cmsc-stageworks/Logic-Re-Initialization-Panel/Mainboard SD Example/Puzzles/AIR_SCRUBBERS/prompt.bmp

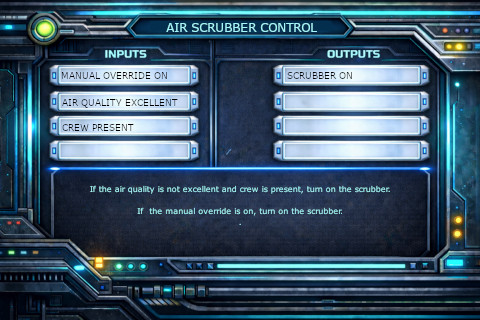
Mainboard SD Example/Puzzles/AIR_SCRUBBERS/prompt.bmp
