cmsc-stageworks/Logic-Re-Initialization-Panel/3D Models/Isolinear Chips NFC/Iso Card Diffuser V2.stl

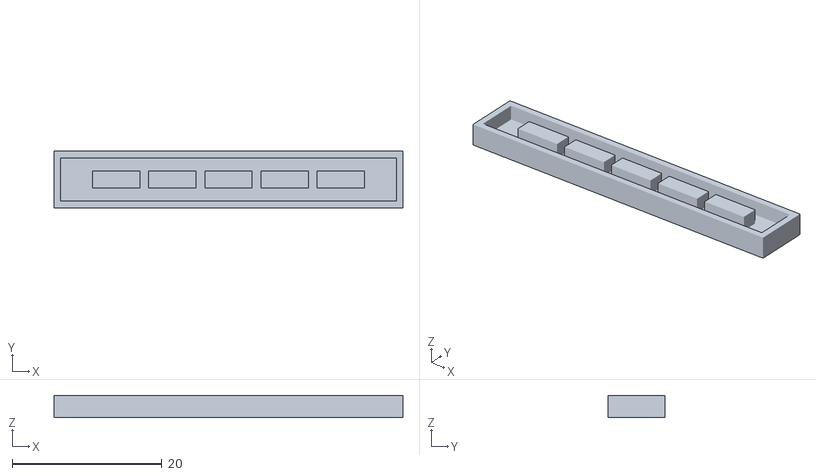
[picture p21: CAD file, 2025-12-29]
3D Models/Isolinear Chips NFC/Iso Card Diffuser V2.stl
46.6 x 7.60 x 3.00
