cmsc-stageworks/Logic-Re-Initialization-Panel/3D Models/Isolinear Chips/PCB REV1.stl

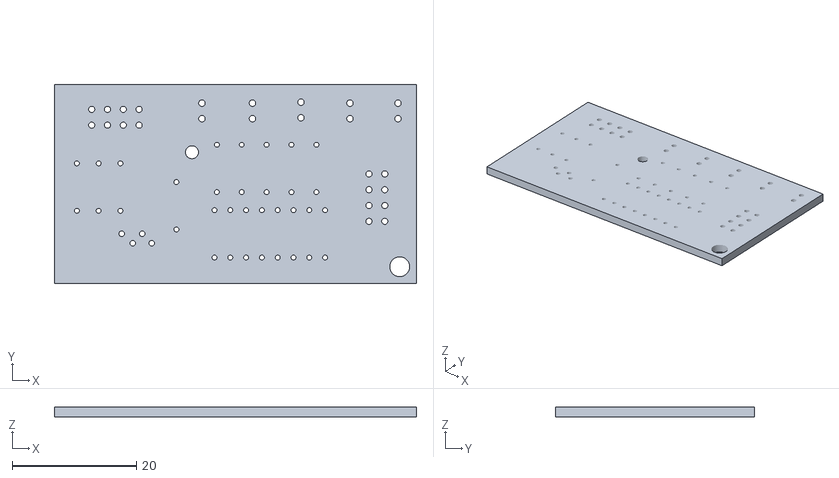
[picture p22: CAD file, 2025-09-20]
3D Models/Isolinear Chips/PCB REV1.stl
58.2 x 32.0 x 1.60
