cmsc-stageworks/Logic-Re-Initialization-Panel/3D Models/Logic Panel/Splitter.stl

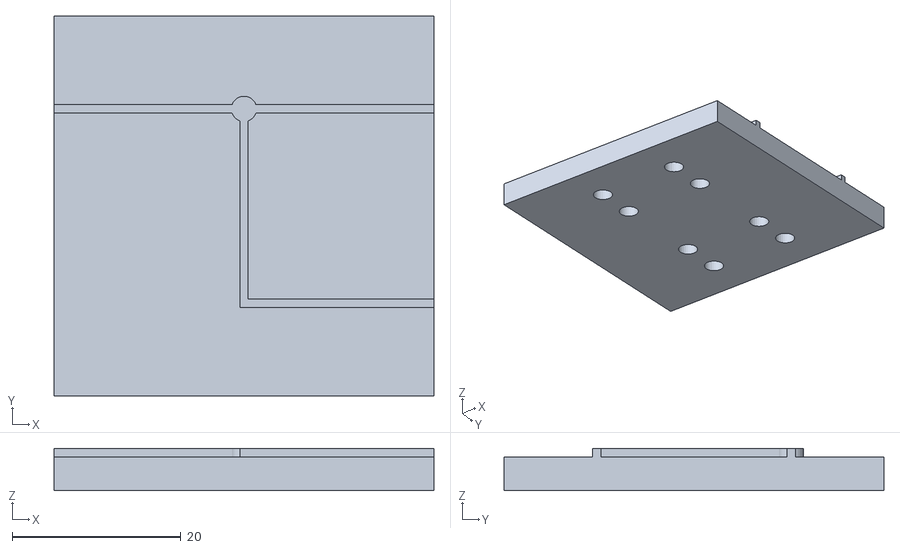
[picture p23: CAD file, 2025-09-20]
3D Models/Logic Panel/Splitter.stl
45.0 x 45.0 x 5.00
