cmsc-stageworks/Logic-Re-Initialization-Panel/Isolinear Chip Board/Isolinear Board PCB/Isolinear Board PCB BARE.step

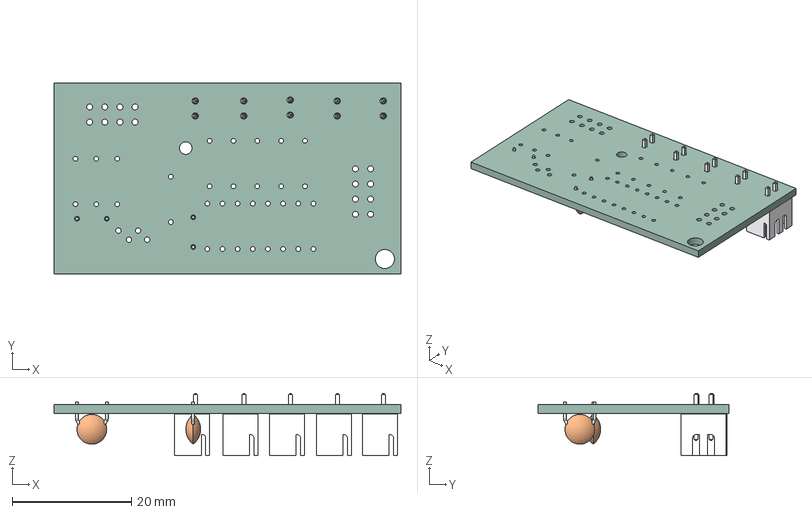
[picture p24: CAD file, 2025-09-20]
Isolinear Chip Board/Isolinear Board PCB/Isolinear Board PCB BARE.step
58.2 x 32.0 x 10.4 mm
JST B2B-XH-A Through-hole shrouded header top entry type x 5
C_Disc_D5.0mm_W2.5mm_P5.00mm x 2
Isolinear Board PCB_PCB
