cmsc-stageworks/Logic-Re-Initialization-Panel/Logic Gates/Logic board magnetic sensor/Logic board magnetic sensor.step

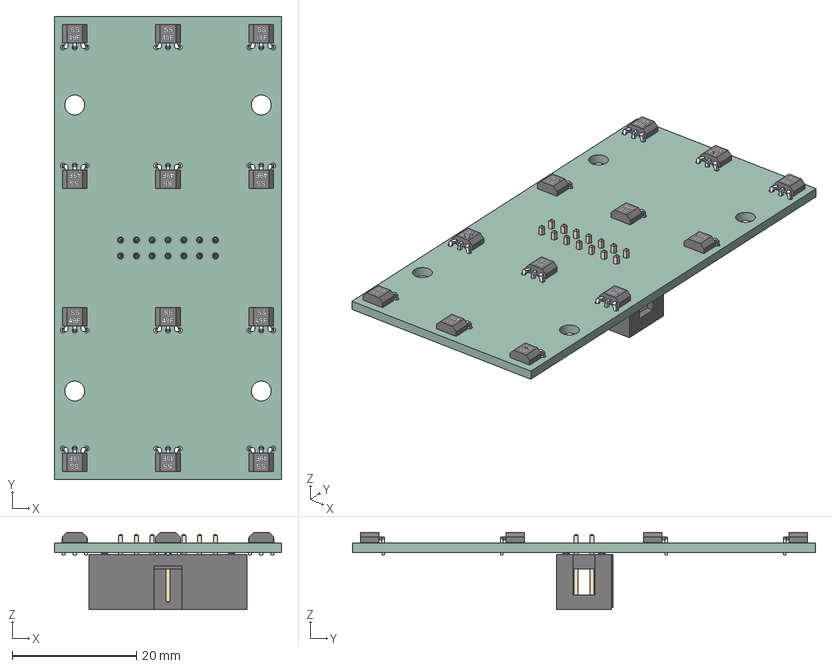
[picture p25: CAD file, 2025-09-20]
Logic Gates/Logic board magnetic sensor/Logic board magnetic sensor.step
36.5 x 74.5 x 12.4 mm
SS49E 90 degree bend x 12
IDC-Header_2x07_P2.54mm_Vertical
Logic board magnetic sensor_PCB
