cmsc-stageworks/Logic-Re-Initialization-Panel/ST7796S Display v7.step

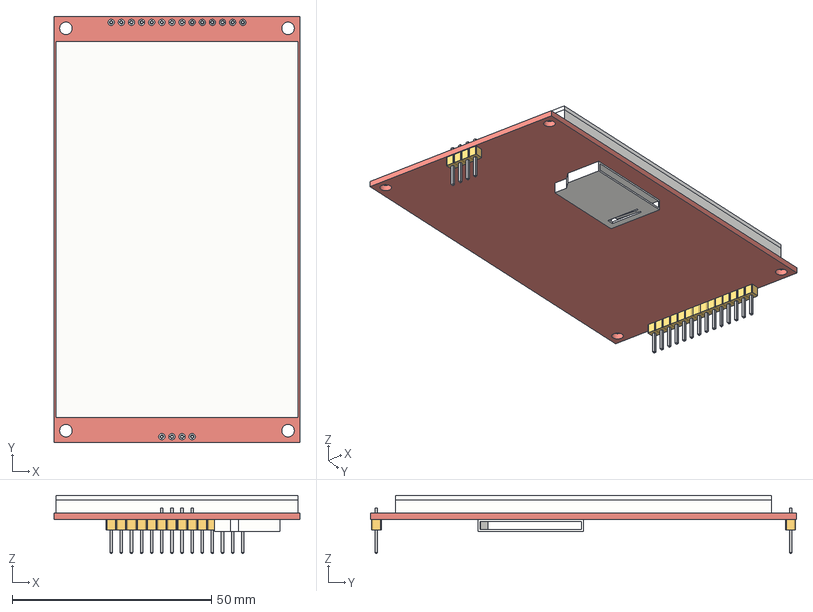
[picture p26: CAD file, 2025-10-08]
ST7796S Display v7.step
61.8 x 107.0 x 14.7 mm
Glass
TFT Screen 480x320
Annular Rings
SD Card
Pins
