cmsc-stageworks/Logic-Re-Initialization-Panel/3D Models/Isolinear Chips/Card Bare Minimum.stl

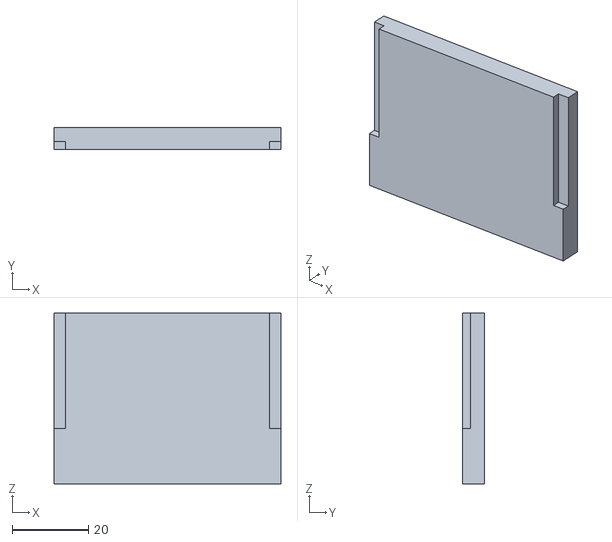
[picture p27: CAD file, 2025-09-20]
3D Models/Isolinear Chips/Card Bare Minimum.stl
59.7 x 5.70 x 44.9
