cmsc-stageworks/Logic-Re-Initialization-Panel/3D Models/Logic Panel/XOR Gate.stl

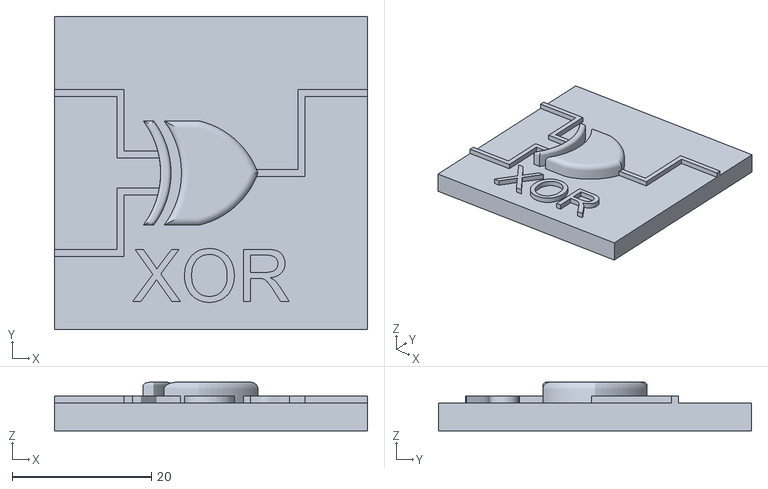
[picture p28: CAD file, 2025-09-20]
3D Models/Logic Panel/XOR Gate.stl
45.0 x 45.0 x 7.00
