cmsc-stageworks/Logic-Re-Initialization-Panel/4 pin female header.step

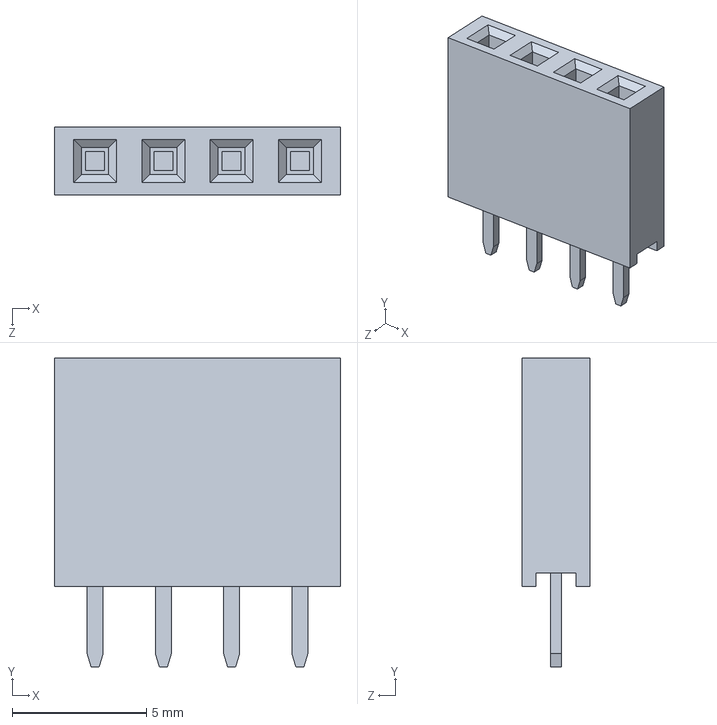
[picture p29: CAD file, 2025-10-08]
4 pin female header.step
10.7 x 11.5 x 2.54 mm
