cmsc-stageworks/Logic-Re-Initialization-Panel/3D Models/Isolinear Chips NFC/Clip.stl

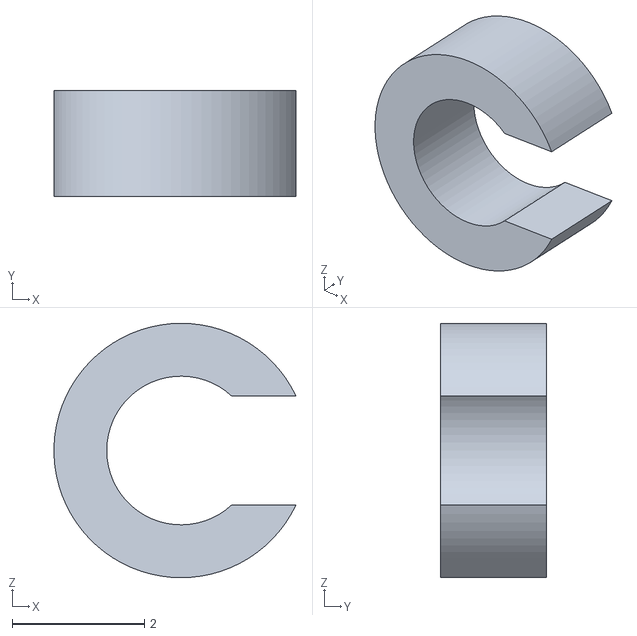
[picture p30: CAD file, 2025-12-28]
3D Models/Isolinear Chips NFC/Clip.stl
3.66 x 1.60 x 3.85
