cmsc-stageworks/Logic-Re-Initialization-Panel/3D Models/Isolinear Chips/Isolinear Chip back.stl

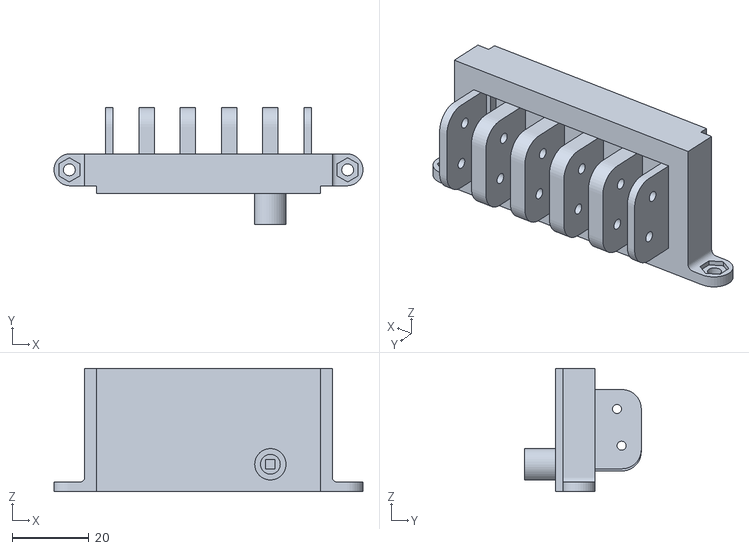
[picture p31: CAD file, 2025-09-20]
3D Models/Isolinear Chips/Isolinear Chip back.stl
80.3 x 30.3 x 32.0
