cmsc-stageworks/Logic-Re-Initialization-Panel/3D Models/Isolinear Chips NFC/Iso Card Print Profile.3mf

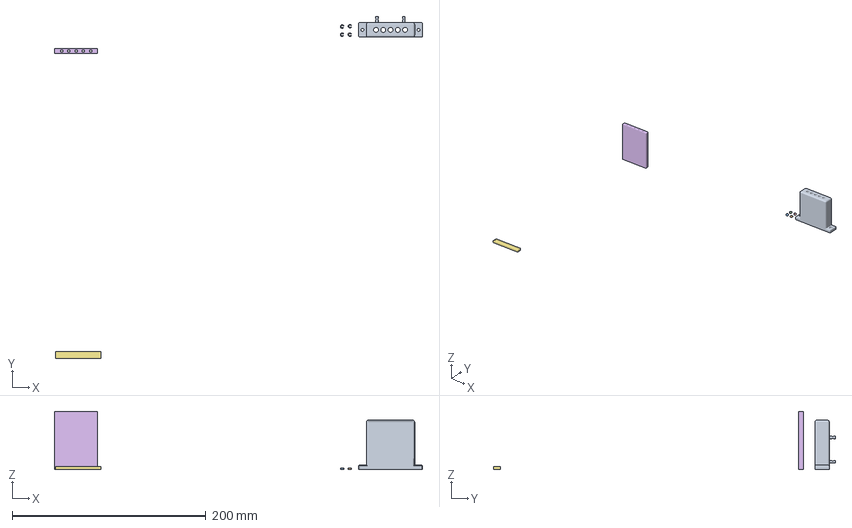
[picture p33: CAD file, 2025-12-28]
3D Models/Isolinear Chips NFC/Iso Card Print Profile.3mf
380.0 x 353.5 x 60.0 mm
Card Holder.stl
Clip.stl x 4
Iso Card Body.stl
Iso Card Diffuser.stl
