cmsc-stageworks/Logic-Re-Initialization-Panel/3D Models/Isolinear Chips NFC/Card Holder.stl

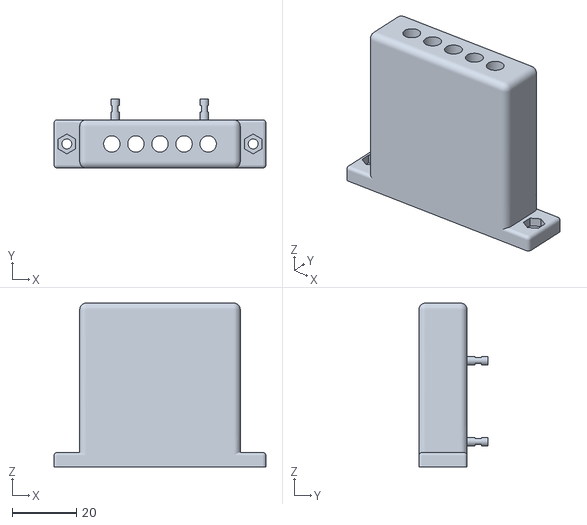
[picture p34: CAD file, 2025-12-28]
3D Models/Isolinear Chips NFC/Card Holder.stl
66.0 x 21.5 x 51.0
