cmsc-stageworks/Logic-Re-Initialization-Panel/3D Models/Isolinear Chips/Card Test.stl

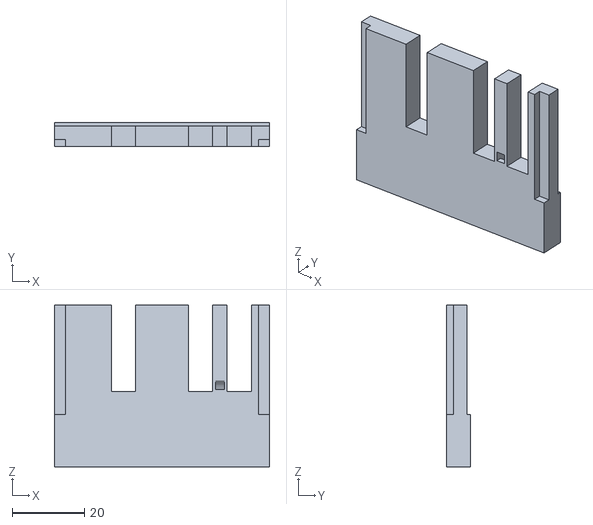
[picture p35: CAD file, 2025-09-20]
3D Models/Isolinear Chips/Card Test.stl
59.7 x 6.70 x 44.9
