cmsc-stageworks/Logic-Re-Initialization-Panel/3D Models/Isolinear Chips/Peg.stl

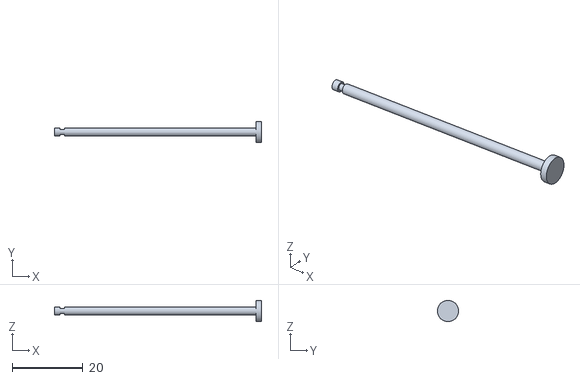
[picture p36: CAD file, 2025-09-20]
3D Models/Isolinear Chips/Peg.stl
58.4 x 6.00 x 6.00
