cmsc-stageworks/Logic-Re-Initialization-Panel/3D Models/Logic Panel/Wire.stl

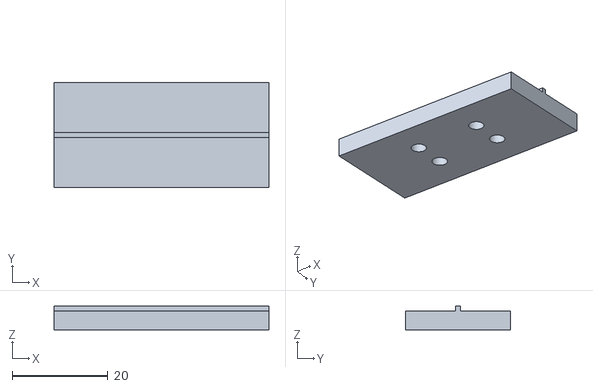
[picture p37: CAD file, 2025-09-20]
3D Models/Logic Panel/Wire.stl
45.0 x 22.0 x 5.00
