cmsc-stageworks/Logic-Re-Initialization-Panel/3D Models/Isolinear Chips/Isolinear Chip back V2.stl

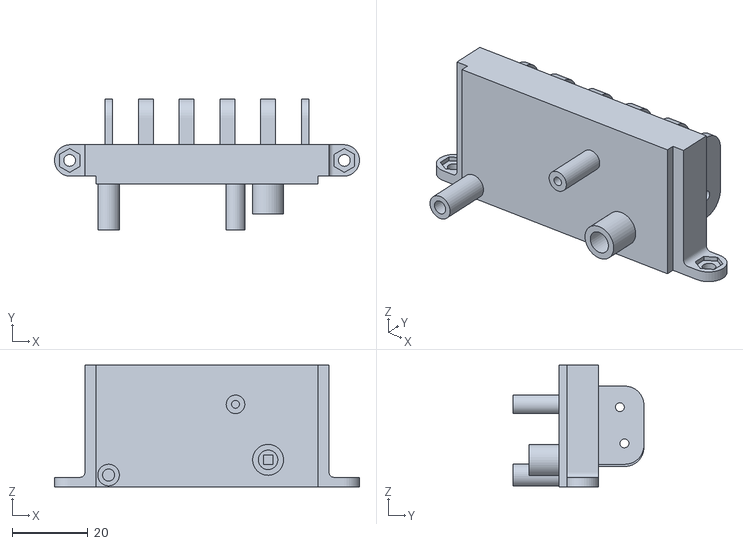
[picture p38: CAD file, 2025-09-20]
3D Models/Isolinear Chips/Isolinear Chip back V2.stl
80.3 x 34.4 x 32.0
