cmsc-stageworks/Logic-Re-Initialization-Panel/3D Models/Logic Panel/Magnet Holder.stl

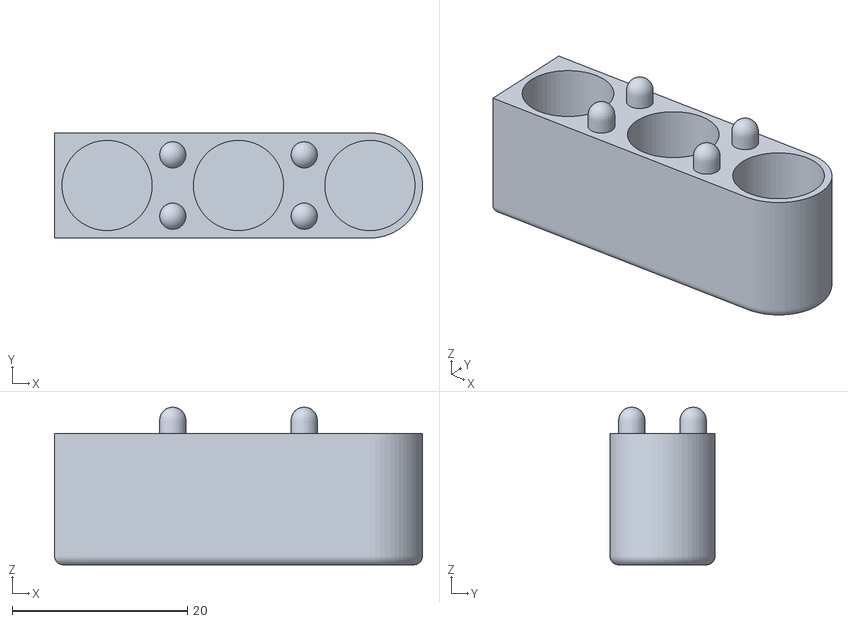
[picture p39: CAD file, 2025-09-20]
3D Models/Logic Panel/Magnet Holder.stl
42.0 x 12.0 x 18.0
