cmsc-stageworks/Logic-Re-Initialization-Panel/3D Models/Logic Panel/Logic puzzle board.stl

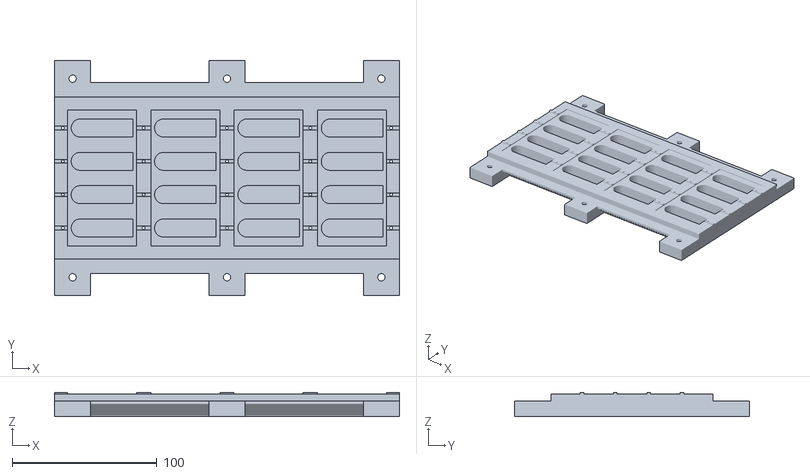
[picture p40: CAD file, 2025-09-20]
3D Models/Logic Panel/Logic puzzle board.stl
238.0 x 162.0 x 16.7
