cmsc-stageworks/Logic-Re-Initialization-Panel/3D Models/Logic Panel/Not Gate.stl

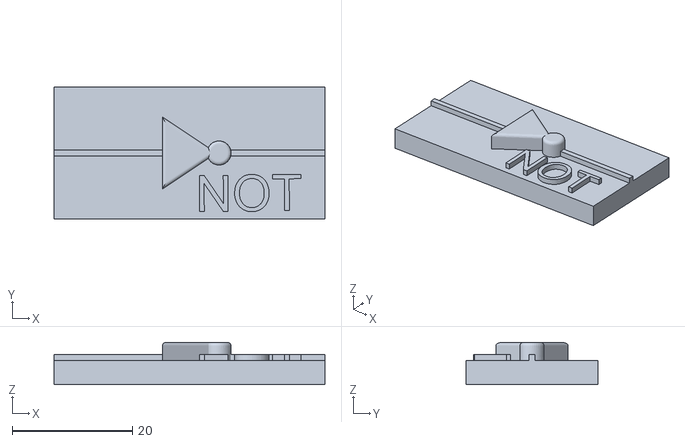
[picture p41: CAD file, 2025-09-20]
3D Models/Logic Panel/Not Gate.stl
45.0 x 22.0 x 7.00
