cmsc-stageworks/Logic-Re-Initialization-Panel/Logic_Re-Initialization_Panel_Code/src/puzzle_manager.h

#ifndef PUZZLE_MANAGER_H
#define PUZZLE_MANAGER_H

#include <Arduino.h>
#include <SdFat.h>
#include <isoCards.h>
#include <MainBoard.h>
#include <Adafruit_GFX.h>
#include <Adafruit_ST7796S.h>
#include <Adafruit_ILI9341.h>
#include <Adafruit_ImageReader.h>
#include <Adafruit_NeoPixel.h>
#include "globalFlags.h"
#include <string.h>
#include "logic_evaluator.h"
#include "logic_wire_lights.h"
#include "cardParser.h"

#define DEBUG_PUZZLE_MANAGER true
#define DEBUG_SHOW_GATE_STATUS false
#define DEBUG_COUNT_LOGIC_INPUTS true

#define PUZZLE_PATH "/Puzzles/"
#define PUZZLE_SOLUTION_FILENAME "sol.txt"
#define PUZZLE_PROMPT_FILENAME "prompt.bmp"
#define PUZZLE_SUCCESS_FILENAME "success.bmp"
#define SOLUTION_FILE_BUFFER_SIZE 512
#define MIN_SOL_FILESIZE 5

#define NUM_ISO_CARDS_LOGIC_PANEL 1
#define LOGIC_GATE_SLOT_NUMBER 0x8888
#define LOGIC_GATE_MUX_NUMBER 1

#define LOGIC_GATES_W 4
#define LOGIC_GATES_H 4
#define LOGIC_GATES_PORTS_USED 4

#define NUM_UI_BTNS 4
#define NUM_LOGIC_INPUTS 4

#define LOGIC_UI_CHIP_NUM 2

#define LOGIC_UI_BTN_BACK 0
#define LOGIC_UI_BTN_SELECT 1
#define LOGIC_UI_BTN_LEFT 2
#define LOGIC_UI_BTN_RIGHT 3

#define LCD_ROTATION 3
#define LCD_H 320
#define LCD_W 480

enum PUZZLE_STATES {
    NOT_IN_PUZZLE,
    IN_PUZZLE,
    INCORRECT_SOLUTION,
    FINISHED_PUZZLE
};

void initPuzzleManager(Adafruit_NeoPixel* strip, uint16_t offset, Adafruit_ST7796S* screen);
void setPuzzleDemoMode(bool isSet);
void tickPuzzleManager();

#endif
